satria-mitra/Cube-Matrix-Visualizer/Components/Cutting parts/Acrylic/cover_acrylic_front.dxf

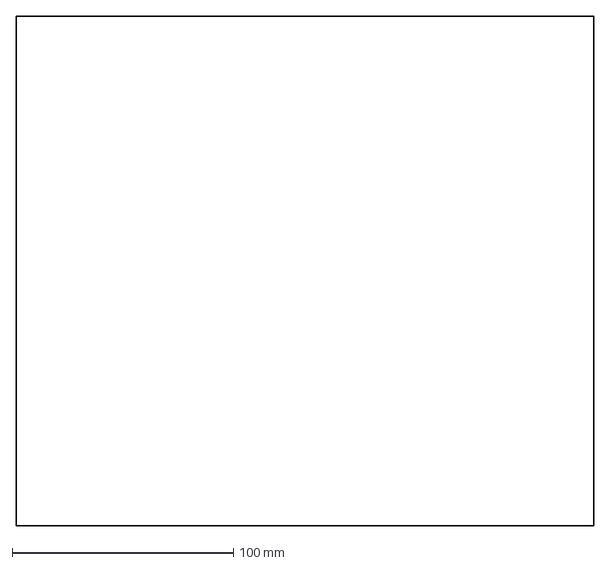
[picture p35: CAD file, 2024-03-18]
Components/Cutting parts/Acrylic/cover_acrylic_front.dxf
261.0 x 230.0 mm
